open-thngs/trap-a-rep-trigger/pcb/components/SKRKAEE020/SKRKAEE020.stp

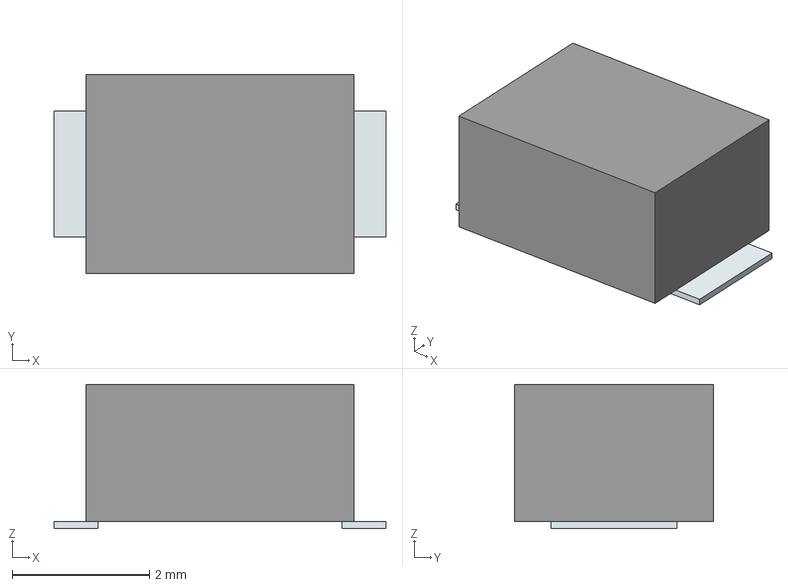
[picture p22: CAD file, 2023-07-13]
pcb/components/SKRKAEE020/SKRKAEE020.stp
4.84 x 2.90 x 2.10 mm
Pins
