open-thngs/trap-a-rep-trigger/pcb/components/USB4105-GF-A/USB4105-GF-A.step

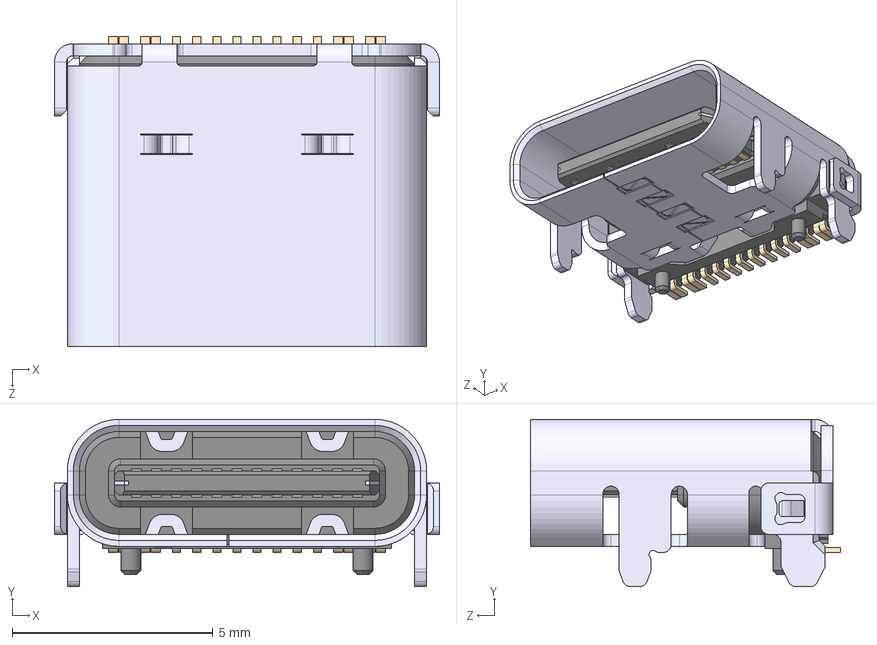
[picture p23: CAD file, 2023-07-05]
pcb/components/USB4105-GF-A/USB4105-GF-A.step
9.58 x 4.16 x 7.71 mm
