open-thngs/trap-a-rep-trigger/pcb/components/VL53L4CD/3D/VL53L4CDV0DH_1.stp

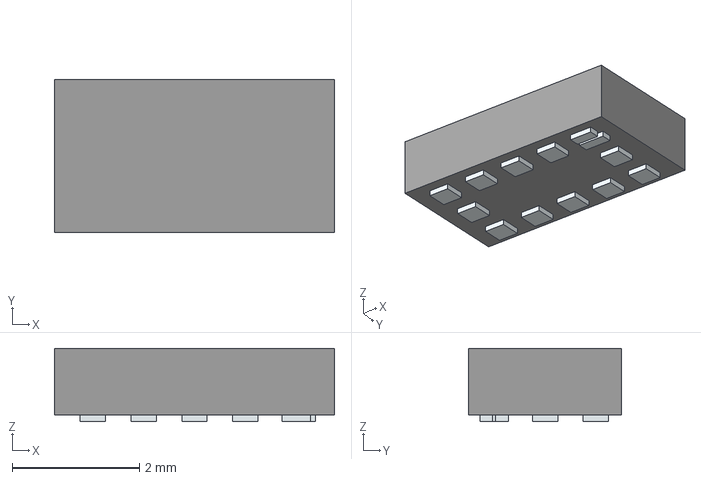
[picture p24: CAD file, 2023-07-05]
pcb/components/VL53L4CD/3D/VL53L4CDV0DH_1.stp
4.40 x 2.40 x 1.15 mm
Pins
