open-thngs/trap-a-rep-trigger/housing/rep-trap-gehaeuse_240506.stp

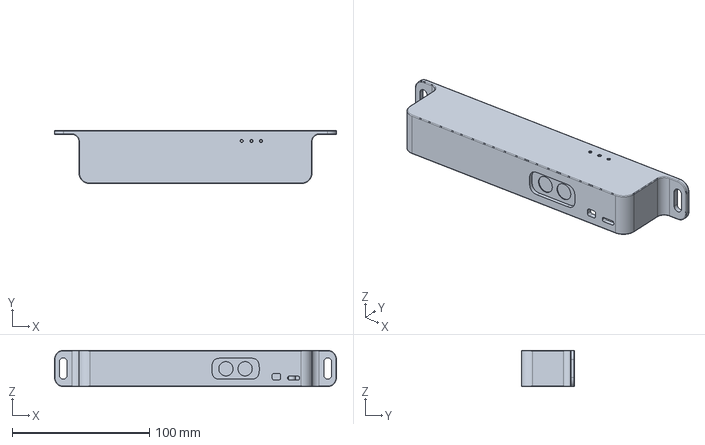
[picture p25: CAD file, 2024-11-06]
housing/rep-trap-gehaeuse_240506.stp
205.3 x 38.8 x 26.5 mm
