open-thngs/trap-a-rep-trigger/pcb/components/APHF1608LSEEQBDZGKC/3D/APHF1608.STEP

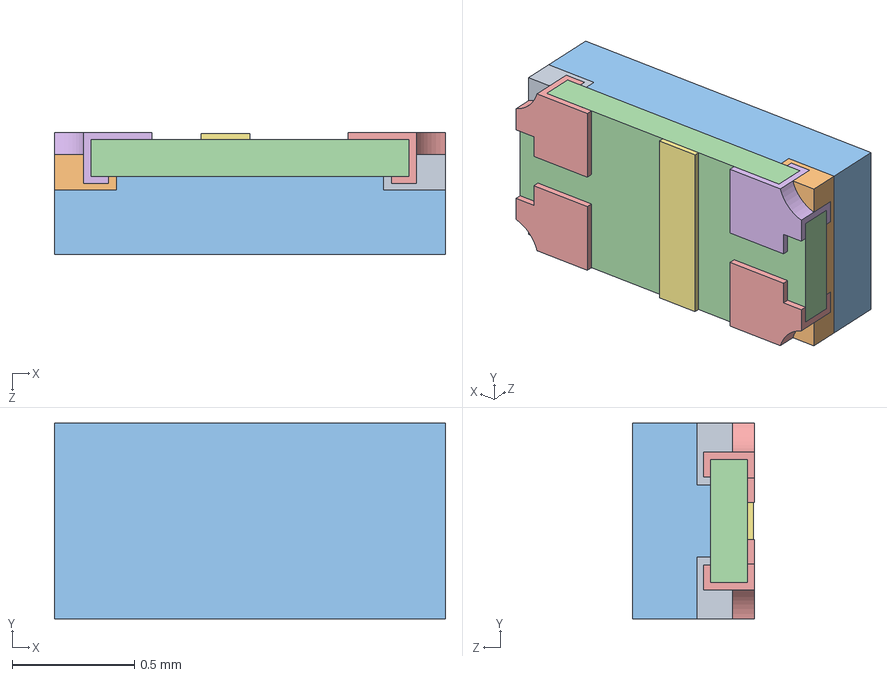
[picture p26: CAD file, 2024-02-12]
pcb/components/APHF1608LSEEQBDZGKC/3D/APHF1608.STEP
1.60 x 0.8 x 0.5 mm
