open-thngs/trap-a-rep-trigger/pcb/components/SKRKAEE020/SKRKAE.STEP

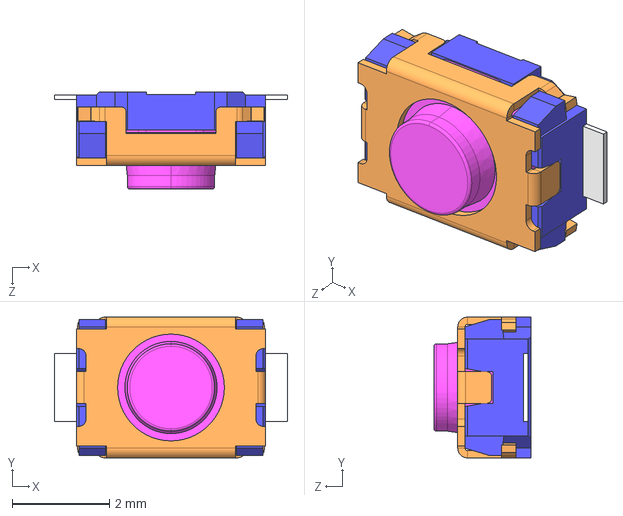
[picture p27: CAD file, 2023-07-13]
pcb/components/SKRKAEE020/SKRKAE.STEP
4.80 x 2.90 x 2.00 mm
