open-thngs/trap-a-rep-trigger/housing/calibration-station.3mf

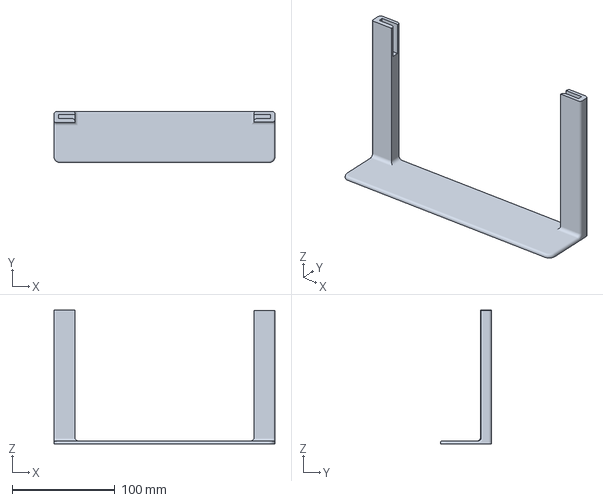
[picture p28: CAD file, 2024-04-17]
housing/calibration-station.3mf
215.0 x 50.0 x 130.3 mm
