open-thngs/trap-a-rep-trigger/housing/glass.stl

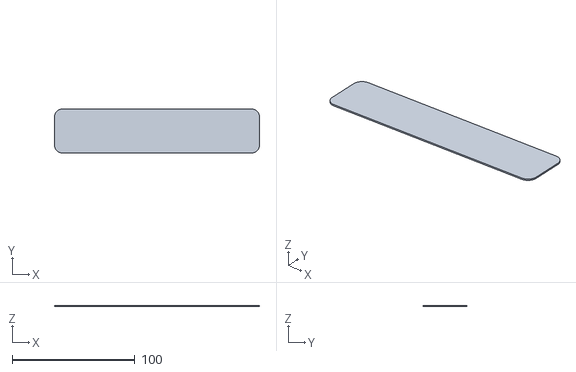
[picture p29: CAD file, 2024-04-08]
housing/glass.stl
166.7 x 35.9 x 1.00
