open-thngs/trap-a-rep-trigger/src/micropython/constants.py

from micropython import const

SOFT_RESET = const(0x0000)
I2C_SLAVE_DEVICE_ADDRESS = const(0x0001)
OSC_FREQUENCY = const(0x0006)
VHV_CONFIG_TIMEOUT_MACROP_LOOP_BOUND = const(0x0008)
XTALK_PLANE_OFFSET_KCPS = const(0x0016)
XTALK_X_PLANE_GRADIENT_KCPS = const(0x0018)
XTALK_Y_PLANE_GRADIENT_KCPS = const(0x001A)
RANGE_OFFSET_MM = const(0x001E)
INNER_OFFSET_MM = const(0x0020)
OUTER_OFFSET_MM = const(0x0022)
GPIO_HV_MUX_CTRL = const(0x0030)
GPIO_TIO_HV_STATUS = const(0x0031)
SYSTEM_INTERRUPT = const(0x0046)
RANGE_CONFIG_A = const(0x005E)
RANGE_CONFIG_B = const(0x0061)
RANGE_CONFIG_SIGMA_THRESH = const(0x0064)
MIN_COUNT_RATE_RTN_LIMIT_MCPS = const(0x0066)
INTERMEASUREMENT_MS = const(0x006C)
THRESH_HIGH = const(0x0072)
THRESH_LOW = const(0x0074)
SYSTEM_INTERRUPT_CLEAR = const(0x0086)
SYSTEM_START = const(0x0087)
RESULT_RANGE_STATUS = const(0x0089)
RESULT_SPAD_NB = const(0x008C)
RESULT_SIGNAL_RATE = const(0x008E)
RESULT_AMBIENT_RATE = const(0x0090)
RESULT_SIGMA = const(0x0092)
RESULT_DISTANCE = const(0x0096)
POWER_GO1 = const(0x0083)
FIRMWARE_ENABLE = const(0x0085)
RESULT_OSC_CALIBRATE_VAL = const(0x00DE)
FIRMWARE_SYSTEM_STATUS = const(0x00E5)
IDENTIFICATION_MODEL_ID = const(0x010F)
SENSOR_CONFIG = const(0x002D)

CLOCK_PPL_FACTOR = 1.065
INTER_MEASUREMENT_FACTOR = 1.055
